nuniesmith/truck-gps/src/stl/v0.5/insert_v5.stl

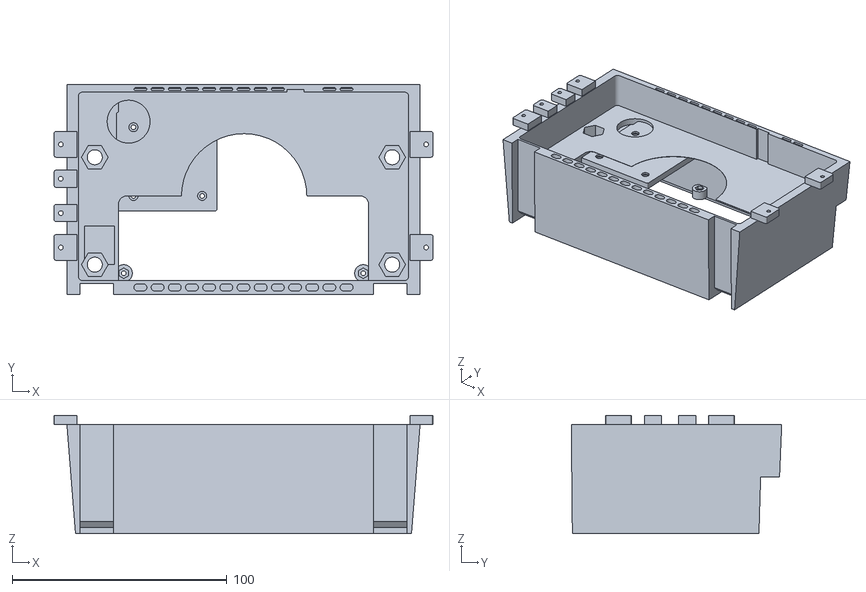
[picture p18: CAD file, 2026-09-27, an earlier design]
src/stl/v0.5/insert_v5.stl
176.5 x 98.0 x 55.0
