nuniesmith/truck-gps/src/stl/v0.5/led_carrier.stl

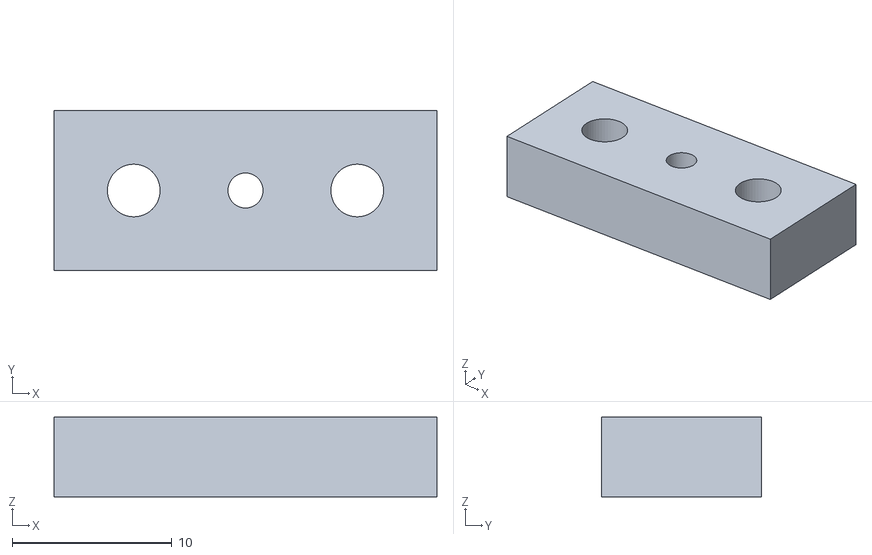
[picture p19: CAD file, 2026-09-27, an earlier design]
src/stl/v0.5/led_carrier.stl
24.0 x 10.0 x 5.00
