nuniesmith/truck-gps/src/stl/v0.5/fan_mount_test.stl

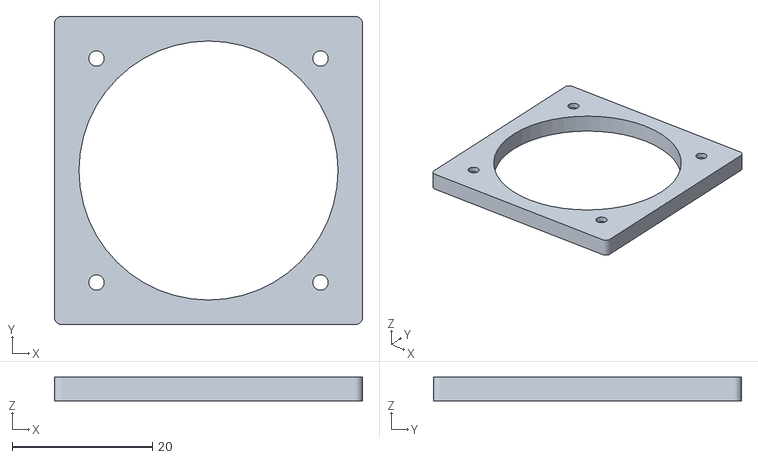
[picture p20: CAD file, 2026-09-27, an earlier design]
src/stl/v0.5/fan_mount_test.stl
44.0 x 44.0 x 3.40
