nuniesmith/truck-gps/src/stl/v0.5/rear_carrier.stl

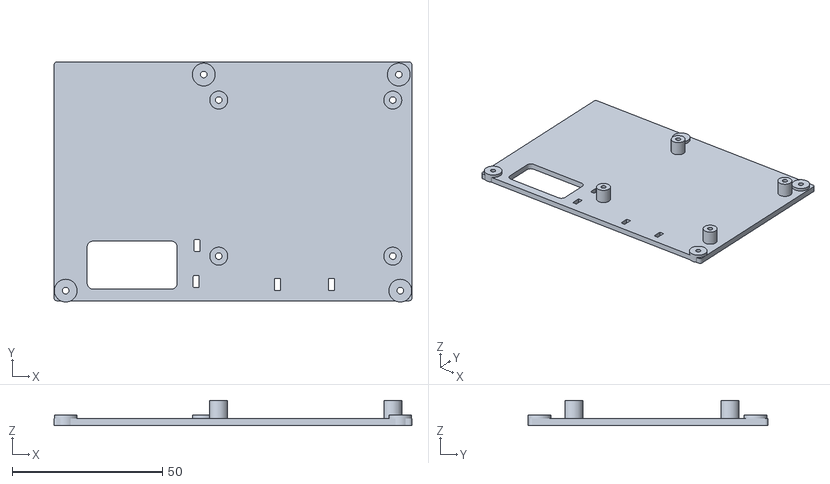
[picture p21: CAD file, 2026-09-27, an earlier design]
src/stl/v0.5/rear_carrier.stl
119.3 x 80.0 x 8.40
